bluetiger9/Breeze-SmartSensorHub/Models/earthquake_data/s2-01-Y-scale-100cms2-300sec.png

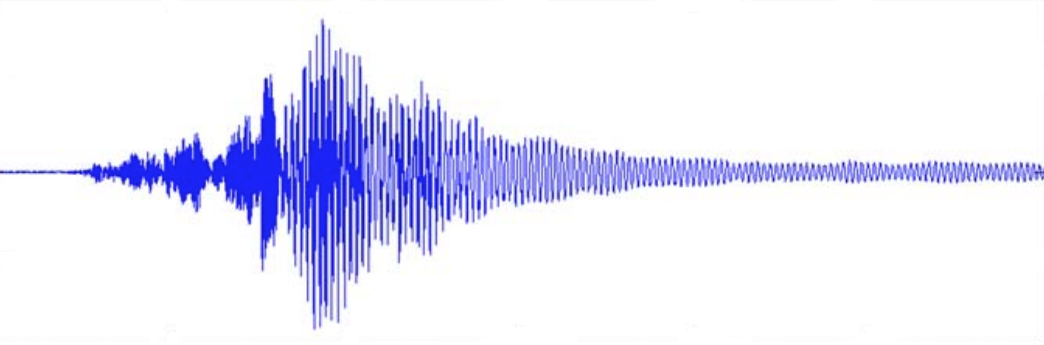
Models/earthquake_data/s2-01-Y-scale-100cms2-300sec.png
