bluetiger9/Breeze-SmartSensorHub/Models/earthquake_data/s1-01-Y-scale-1G-60sec.png

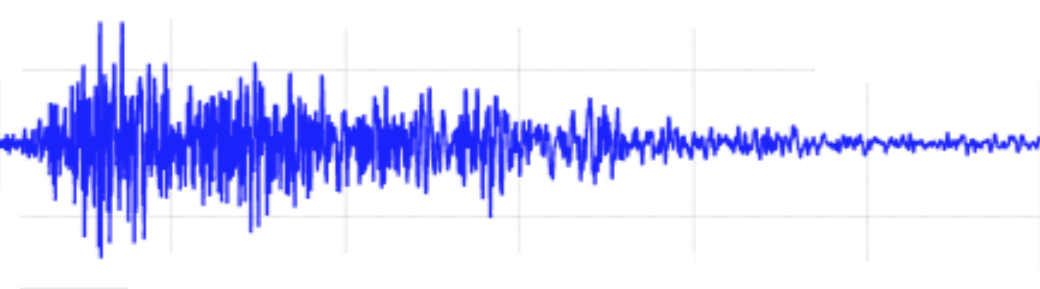
Models/earthquake_data/s1-01-Y-scale-1G-60sec.png
