bluetiger9/Breeze-SmartSensorHub/Models/earthquake_data/s1-02-X-scale-0.4G-60sec.png

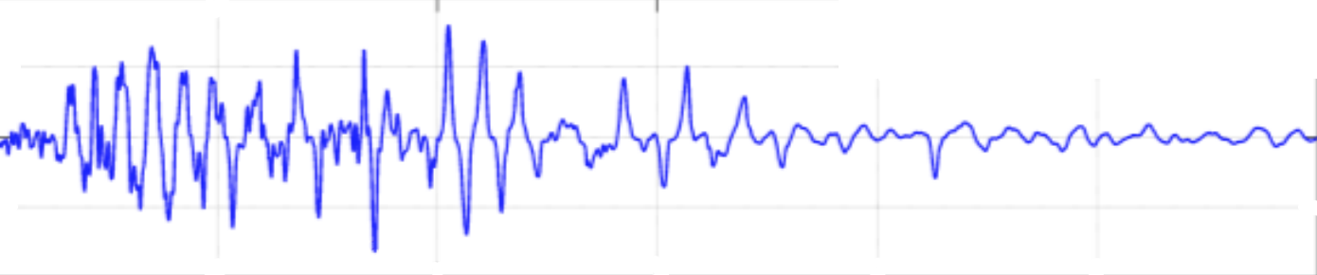
Models/earthquake_data/s1-02-X-scale-0.4G-60sec.png
