bluetiger9/Breeze-SmartSensorHub/Models/earthquake_data/s1-02-Z-scale-0.2G-60sec.png

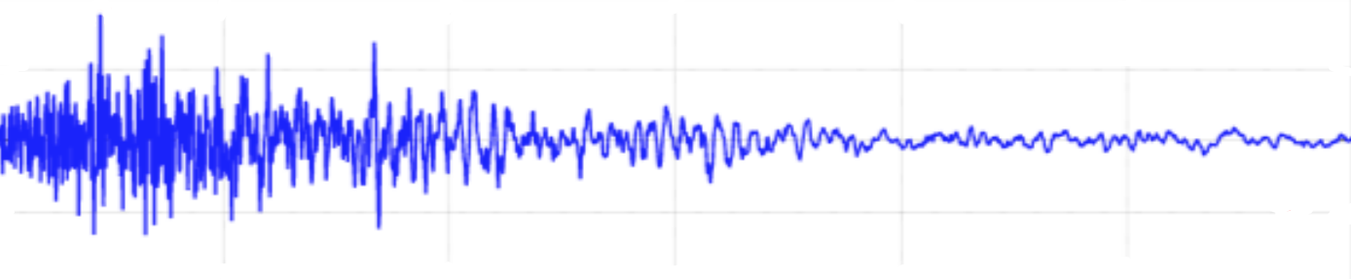
Models/earthquake_data/s1-02-Z-scale-0.2G-60sec.png
