bluetiger9/Breeze-SmartSensorHub/Models/earthquake_data/s3-01-Y-scale-0.34cms2-120sec.png

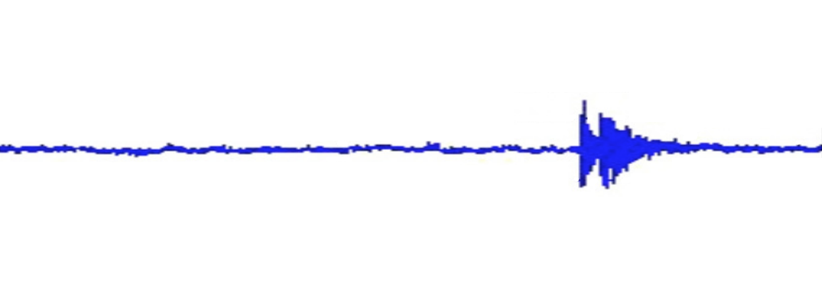
Models/earthquake_data/s3-01-Y-scale-0.34cms2-120sec.png
