bluetiger9/Breeze-SmartSensorHub/Models/earthquake_data/s4-02-XYZ-scale-0.75g-50sec.png

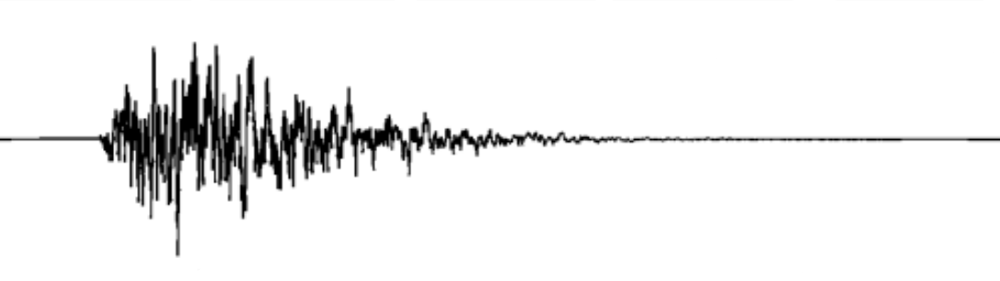
Models/earthquake_data/s4-02-XYZ-scale-0.75g-50sec.png
