bluetiger9/Breeze-SmartSensorHub/Models/earthquake_data/s5-01-Z-scale-150cms2-70sec.png

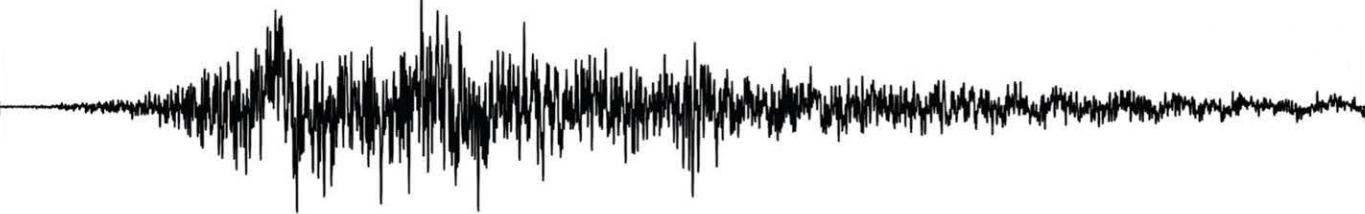
Models/earthquake_data/s5-01-Z-scale-150cms2-70sec.png
