bluetiger9/Breeze-SmartSensorHub/Models/earthquake_data/s5-02-X-scale-150cms2-70sec.png

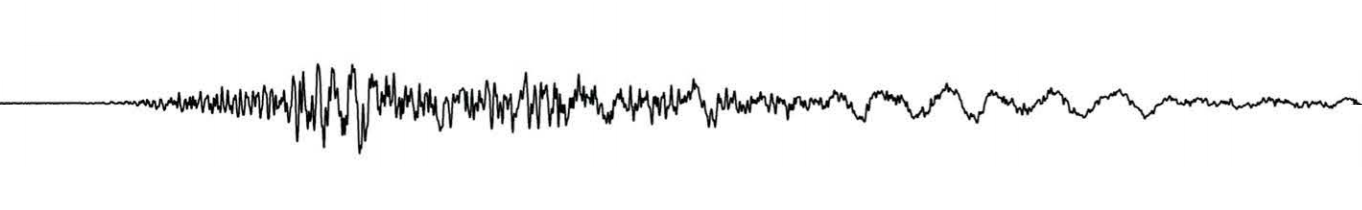
Models/earthquake_data/s5-02-X-scale-150cms2-70sec.png
