bluetiger9/Breeze-SmartSensorHub/Firmware/inc/fpga_gpio_top_bit.h

#include <stdint.h>

uint32_t	axFPGABitStream_GPIO[] = {
	0x00000000, 0x00000000, 0x00000000, 0x00000000, 0x00000000, 0x00000000, 0x00000000, 0x00000000, 0x00000000, 0x00000020, 
	0x00000000, 0x00000000, 0x00000000, 0x00000000, 0x00000020, 0x00000000, 0x00000000, 0x00000000, 0x00000000, 0x00000000, 
	0x00000000, 0x00000000, 0x00000000, 0x00000000, 0x00000000, 0x00000000, 0x00000000, 0x00000000, 0x00000000, 0x00000000, 
	0x00000000, 0x00000000, 0x00000000, 0x00000000, 0x00000000, 0x00000000, 0x00000000, 0x00000020, 0x00000000, 0x00000000, 
	0x00000000, 0x00000000, 0x00000000, 0x00000000, 0x00000000, 0x00000080, 0x00000000, 0x00000000, 0x00000000, 0x00000000, 
	0x00000000, 0x00000000, 0x00000000, 0x00000000, 0x00000000, 0x00000000, 0x00000000, 0x00000000, 0x00000000, 0x00000000, 
	0x00000000, 0x00000000, 0x00000000, 0x00000000, 0x00000000, 0x00000000, 0x00000000, 0x00000000, 0x00000000, 0x00000000, 
	0x00000000, 0x00000000, 0x00000000, 0x00000000, 0x00000000, 0x00000000, 0x00000000, 0x00000000, 0x00000000, 0x00000000, 
	0x00000000, 0x00000000, 0x00000000, 0x00000000, 0x00000000, 0x00000000, 0x00000000, 0x00000000, 0x00000000, 0x00000000, 
	0x00000000, 0x00000000, 0x00000000, 0x00000000, 0x00000000, 0x00000000, 0x00000008, 0x00000000, 0x00000000, 0x00000000, 
	0x00000000, 0x00000000, 0x00000002, 0x00000004, 0x00000004, 0x00000000, 0x00000000, 0x00000002, 0x00000000, 0x00000000, 
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
	0x40004c5c, 0x00000830,
	0x40004c60, 0x00000830,
	0x40004c64, 0x00000830,
	0x40004c68, 0x00000830,
	0x40004c6c, 0x00000830,
	0x40004c70, 0x00000830,
	0x40004c74, 0x00000830,
	0x40004c78, 0x00000830,
	0x40004c7c, 0x00000830,
	0x40004d80, 0xffffffff,
	0x40004d84, 0x00000000
};
