bluetiger9/Breeze-SmartSensorHub/Firmware/src/pincfg_table.c

/*==========================================================
 * Copyright 2020 QuickLogic Corporation
 *
 * Licensed under the Apache License, Version 2.0 (the "License");
 * you may not use this file except in compliance with the License.
 * You may obtain a copy of the License at
 *
 *    http://www.apache.org/licenses/LICENSE-2.0
 *
 * Unless required by applicable law or agreed to in writing, software
 * distributed under the License is distributed on an "AS IS" BASIS,
 * WITHOUT WARRANTIES OR CONDITIONS OF ANY KIND, either express or implied.
 * See the License for the specific language governing permissions and
 * limitations under the License.
 *==========================================================*/

#include "Fw_global_config.h"
#include "eoss3_hal_pad_config.h"
#include "eoss3_hal_gpio.h"

PadConfig pincfg_table[] = 
{
  { // setup UART TX
    .ucPin = PAD_44,
    .ucFunc = PAD44_FUNC_SEL_UART_TXD,
    .ucCtrl = PAD_CTRL_SRC_A0,
    .ucMode = PAD_MODE_OUTPUT_EN,
    .ucPull = PAD_NOPULL,
    .ucDrv = PAD_DRV_STRENGHT_4MA,
    .ucSpeed = PAD_SLEW_RATE_SLOW,
    .ucSmtTrg = PAD_SMT_TRIG_DIS,
  },
  { // setup UART RX
    .ucPin = PAD_45,                     // Options: 14, 16, 25, or 45
    .ucFunc = PAD45_FUNC_SEL_UART_RXD,
    .ucCtrl = PAD_CTRL_SRC_A0,
    .ucMode = PAD_MODE_INPUT_EN,
    .ucPull = PAD_NOPULL,
  },



  { // setup debug input pins Pad 14 - S3_SW_DP_CLK
    .ucMode = PAD_MODE_INPUT_EN,
    .ucCtrl = PAD_CTRL_SRC_OTHER,
    .ucDrv = PAD_DRV_STRENGHT_4MA,
    .ucSpeed = PAD_SLEW_RATE_SLOW,
    .ucSmtTrg = PAD_SMT_TRIG_DIS,
    .ucPin = PAD_14,
    .ucFunc = PAD14_FUNC_SEL_SW_DP_CLK,
    .ucPull = PAD_NOPULL,
  },

  { //setup debug input pins Pad 15 - S3_SW_DP_IO
    .ucMode = PAD_MODE_INPUT_EN,
    .ucCtrl = PAD_CTRL_SRC_OTHER,
    .ucDrv = PAD_DRV_STRENGHT_4MA,
    .ucSpeed = PAD_SLEW_RATE_SLOW,
    .ucSmtTrg = PAD_SMT_TRIG_DIS,
    .ucPin = PAD_15,
    .ucFunc = PAD15_FUNC_SEL_SW_DP_IO,
    .ucPull = PAD_NOPULL
  },

  {
    //Currently Pad 9 is not configured and has an internal pull-down and is 
    // connected to SWD_DATA that has an external pull-up
    //Pad 9 - remove default pull-down configuration, ensure pin is configured as input
    .ucPin = PAD_9,
    .ucFunc = PAD9_FUNC_SEL_GPIO_1,
    .ucMode = PAD_MODE_INPUT_EN,
    .ucPull = PAD_NOPULL,
    .ucDrv = PAD_DRV_STRENGHT_4MA,
    .ucSpeed = PAD_SLEW_RATE_SLOW,
    .ucSmtTrg = PAD_SMT_TRIG_DIS
  },
#if 0
  {  // configure SCL0
    .ucPin = PAD_0,
    .ucFunc = PAD0_FUNC_SEL_SCL_0,
    .ucCtrl = PAD_CTRL_SRC_OTHER,
    .ucMode = PAD_MODE_INPUT_EN,
    .ucPull = PAD_PULLUP,
    .ucDrv = PAD_DRV_STRENGHT_4MA,
    .ucSpeed = PAD_SLEW_RATE_SLOW,
    .ucSmtTrg = PAD_SMT_TRIG_DIS,
  },

  {  // configure SDA0
    .ucPin = PAD_1,
    .ucFunc = PAD1_FUNC_SEL_SDA_0,
    .ucCtrl = PAD_CTRL_SRC_OTHER,
    .ucMode = PAD_MODE_INPUT_EN,
    .ucPull = PAD_PULLUP,
    .ucDrv = PAD_DRV_STRENGHT_4MA,
    .ucSpeed = PAD_SLEW_RATE_SLOW,
    .ucSmtTrg = PAD_SMT_TRIG_DIS,
  },
#endif
  // LEDS
//   { // setup blue LED
//    .ucPin = PAD_18,
//    .ucFunc = PAD18_FUNC_SEL_GPIO_4,
//    .ucCtrl = PAD_CTRL_SRC_A0,
//    .ucMode = PAD_MODE_OUTPUT_EN,
//    .ucPull = PAD_NOPULL,
//    .ucDrv = PAD_DRV_STRENGTH_4MA,
//    .ucSpeed = PAD_SLEW_RATE_SLOW,
//    .ucSmtTrg = PAD_SMT_TRIG_DIS,
//  },
  { // setup green LED
    .ucPin = PAD_21,
    .ucFunc = PAD21_FUNC_SEL_GPIO_5,
    .ucCtrl = PAD_CTRL_SRC_A0,
    .ucMode = PAD_MODE_OUTPUT_EN,
    .ucPull = PAD_NOPULL,
    .ucDrv = PAD_DRV_STRENGTH_4MA,
    .ucSpeed = PAD_SLEW_RATE_SLOW,
    .ucSmtTrg = PAD_SMT_TRIG_DIS,
  },
  { // setup red LED
    .ucPin = PAD_22,
    .ucFunc = PAD22_FUNC_SEL_GPIO_6,
    .ucCtrl = PAD_CTRL_SRC_A0,
    .ucMode = PAD_MODE_OUTPUT_EN,
    .ucPull = PAD_NOPULL,
    .ucDrv = PAD_DRV_STRENGTH_4MA,
    .ucSpeed = PAD_SLEW_RATE_SLOW,
    .ucSmtTrg = PAD_SMT_TRIG_DIS,
  },
  
//   {
//    // Pad6 is the user button
//    .ucPin = PAD_6,
//    .ucFunc = PAD6_FUNC_SEL_GPIO_0,
//    .ucMode = PAD_MODE_INPUT_EN,
//    .ucPull = PAD_PULLUP,
//    .ucDrv = PAD_DRV_STRENGTH_4MA,
//    .ucSpeed = PAD_SLEW_RATE_SLOW,
//    .ucSmtTrg = PAD_SMT_TRIG_DIS
//  },

  
   { // Pad 33 -- Test clock
    .ucPin = PAD_33,
    .ucFunc = PAD33_FUNC_SEL_FBIO_33,
    .ucCtrl = PAD_CTRL_SRC_FPGA,
    .ucMode = PAD_MODE_OUTPUT_EN,
    .ucPull = PAD_NOPULL,
    .ucDrv = PAD_DRV_STRENGHT_4MA,
    .ucSpeed = PAD_SLEW_RATE_SLOW,
    .ucSmtTrg = PAD_SMT_TRIG_DIS,
  },
  
  // SPI Master
   { // Pad 34 -- SPI Master CLK
    .ucPin = PAD_34,
    .ucFunc = PAD34_FUNC_SEL_FBIO_34,
    .ucCtrl = PAD_CTRL_SRC_FPGA,
    .ucMode = PAD_MODE_OUTPUT_EN,
    .ucPull = PAD_NOPULL,
    .ucDrv = PAD_DRV_STRENGHT_4MA,
    .ucSpeed = PAD_SLEW_RATE_SLOW,
    .ucSmtTrg = PAD_SMT_TRIG_DIS,
  },
  { // Pad 38 -- SPI Master MOSI
    .ucPin = PAD_38,
    .ucFunc = PAD38_FUNC_SEL_FBIO_38,
    .ucCtrl = PAD_CTRL_SRC_FPGA,
    .ucMode = PAD_MODE_OUTPUT_EN,
    .ucPull = PAD_NOPULL,
    .ucDrv = PAD_DRV_STRENGHT_4MA,
    .ucSpeed = PAD_SLEW_RATE_SLOW,
    .ucSmtTrg = PAD_SMT_TRIG_DIS,
  },
  { // Pad 39 -- SPI Master SSn1
    .ucPin = PAD_39,
    .ucFunc = PAD39_FUNC_SEL_FBIO_39,
    .ucCtrl = PAD_CTRL_SRC_FPGA,
    .ucMode = PAD_MODE_OUTPUT_EN,
    .ucPull = PAD_NOPULL,
    .ucDrv = PAD_DRV_STRENGHT_4MA,
    .ucSpeed = PAD_SLEW_RATE_SLOW,
    .ucSmtTrg = PAD_SMT_TRIG_DIS,
  },
   { // Pad 36 -- SPI Master MISO
    .ucPin = PAD_36,
    .ucFunc = PAD36_FUNC_SEL_FBIO_36,
    .ucCtrl = PAD_CTRL_SRC_FPGA,
    .ucMode = PAD_MODE_INPUT_EN,
    .ucPull = PAD_NOPULL,
  },
  
  //------------- USB ---------------//
   { // Pad 37 -- USB Pullup control
    .ucPin = PAD_37,
    .ucFunc = PAD37_FUNC_SEL_FBIO_37,
    .ucCtrl = PAD_CTRL_SRC_FPGA,
    .ucMode = PAD_MODE_OUTPUT_EN,
    .ucPull = PAD_NOPULL,
    .ucDrv = PAD_DRV_STRENGHT_4MA,
    .ucSpeed = PAD_SLEW_RATE_SLOW,
    .ucSmtTrg = PAD_SMT_TRIG_DIS,
  },
  { // Pad 41 -- USB D-
    .ucPin = PAD_41,
    .ucFunc = PAD41_FUNC_SEL_FBIO_41,
    .ucCtrl = PAD_CTRL_SRC_FPGA,
    .ucMode = PAD_MODE_OUTPUT_EN,
    .ucPull = PAD_NOPULL,
    .ucDrv = PAD_DRV_STRENGHT_4MA,
    .ucSpeed = PAD_SLEW_RATE_SLOW,
    .ucSmtTrg = PAD_SMT_TRIG_DIS,
  },
  { // Pad 41 -- USB D+
    .ucPin = PAD_42,
    .ucFunc = PAD42_FUNC_SEL_FBIO_42,
    .ucCtrl = PAD_CTRL_SRC_FPGA,
    .ucMode = PAD_MODE_OUTPUT_EN,
    .ucPull = PAD_NOPULL,
    .ucDrv = PAD_DRV_STRENGHT_4MA,
    .ucSpeed = PAD_SLEW_RATE_SLOW,
    .ucSmtTrg = PAD_SMT_TRIG_DIS,
  },

#if (SENSOR_SSSS_RATE_DEBUG_GPIO)
  { // setup GPIO for toggling whenever a datablock is dispatched to UART
    .ucPin = PAD_11,
    .ucFunc = PAD11_FUNC_SEL_GPIO_2,
    .ucCtrl = PAD_CTRL_SRC_A0,
    .ucMode = PAD_MODE_OUTPUT_EN,
    .ucPull = PAD_NOPULL,
    .ucDrv = PAD_DRV_STRENGTH_4MA,
    .ucSpeed = PAD_SLEW_RATE_SLOW,
    .ucSmtTrg = PAD_SMT_TRIG_DIS,
  },
#else
  { // IO_11 / GPIO(2) - CS_AQ
    .ucPin = PAD_11,
    .ucFunc = PAD11_FUNC_SEL_GPIO_2,
    .ucCtrl = PAD_CTRL_SRC_A0,
    .ucMode = PAD_MODE_OUTPUT_EN,
    .ucPull = PAD_NOPULL,
    .ucDrv = PAD_DRV_STRENGTH_4MA,
    .ucSpeed = PAD_SLEW_RATE_SLOW,
    .ucSmtTrg = PAD_SMT_TRIG_DIS,
  },
#endif
  { // IO_30 / GPIO(3) - CS_UV
    .ucPin = PAD_30,
    .ucFunc = PAD30_FUNC_SEL_GPIO_3,
    .ucCtrl = PAD_CTRL_SRC_A0,
    .ucMode = PAD_MODE_OUTPUT_EN,
    .ucPull = PAD_NOPULL,
    .ucDrv = PAD_DRV_STRENGTH_4MA,
    .ucSpeed = PAD_SLEW_RATE_SLOW,
    .ucSmtTrg = PAD_SMT_TRIG_DIS,
  },
  { // IO_24 / GPIO(0) - CS_COM
    .ucPin = PAD_24,
    .ucFunc = PAD24_FUNC_SEL_GPIO_0,
    .ucCtrl = PAD_CTRL_SRC_A0,
    .ucMode = PAD_MODE_OUTPUT_EN,
    .ucPull = PAD_NOPULL,
    .ucDrv = PAD_DRV_STRENGTH_4MA,
    .ucSpeed = PAD_SLEW_RATE_SLOW,
    .ucSmtTrg = PAD_SMT_TRIG_DIS,
  },
  { // IO_23 / GPIO(7) - CS_COM (??? - hangging)
    .ucPin = PAD_23,
    .ucFunc = PAD23_FUNC_SEL_GPIO_7,
    .ucCtrl = PAD_CTRL_SRC_A0,
    .ucMode = PAD_MODE_OUTPUT_EN,
    .ucPull = PAD_NOPULL,
    .ucDrv = PAD_DRV_STRENGTH_4MA,
    .ucSpeed = PAD_SLEW_RATE_SLOW,
    .ucSmtTrg = PAD_SMT_TRIG_DIS,
  },
  { // IO_24 / GPIO(0) - CS_COM
    .ucPin = PAD_31,
    .ucFunc = PAD31_FUNC_SEL_GPIO_4,
    .ucCtrl = PAD_CTRL_SRC_A0,
    .ucMode = PAD_MODE_OUTPUT_EN,
    .ucPull = PAD_NOPULL,
    .ucDrv = PAD_DRV_STRENGTH_4MA,
    .ucSpeed = PAD_SLEW_RATE_SLOW,
    .ucSmtTrg = PAD_SMT_TRIG_DIS,
  },

  { // IO_2 / FBIO(2) - PWR_COM
    .ucPin = PAD_2,
    .ucFunc = PAD2_FUNC_SEL_FBIO_2,
    .ucCtrl = PAD_CTRL_SRC_FPGA,
    .ucMode = PAD_MODE_OUTPUT_EN,
    .ucPull = PAD_NOPULL,
    .ucDrv = PAD_DRV_STRENGTH_4MA,
    .ucSpeed = PAD_SLEW_RATE_SLOW,
    .ucSmtTrg = PAD_SMT_TRIG_DIS,
  },

  { // IO_12 / FBIO(12) - PWR_COM
    .ucPin = PAD_12,
    .ucFunc = PAD12_FUNC_SEL_FBIO_12,
    .ucCtrl = PAD_CTRL_SRC_FPGA,
    .ucMode = PAD_MODE_OUTPUT_EN,
    .ucPull = PAD_NOPULL,
    .ucDrv = PAD_DRV_STRENGTH_4MA,
    .ucSpeed = PAD_SLEW_RATE_SLOW,
    .ucSmtTrg = PAD_SMT_TRIG_DIS,
  },

#if (AUDIO_DRIVER == 1) && (PDM_PAD_28_29 == 1)
  { // Pad 28 -- PDM DATA
    .ucPin = PAD_28,
    .ucFunc = PAD28_FUNC_SEL_PDM_DIN,
    .ucCtrl = PAD_CTRL_SRC_A0,
    .ucMode = PAD_MODE_INPUT_EN,
    .ucPull = PAD_NOPULL,
    .ucDrv = PAD_DRV_STRENGHT_4MA,
    .ucSpeed = PAD_SLEW_RATE_SLOW,
    .ucSmtTrg = PAD_SMT_TRIG_DIS,
  },
  { // Pad 29 -- PDM CLK
    .ucPin = PAD_29,
    .ucFunc = PAD29_FUNC_SEL_PDM_CKO,
    .ucCtrl = PAD_CTRL_SRC_A0,
    .ucMode = PAD_MODE_OUTPUT_EN,
    .ucPull = PAD_NOPULL,
    .ucDrv = PAD_DRV_STRENGHT_4MA,
    .ucSpeed = PAD_SLEW_RATE_SLOW,
    .ucSmtTrg = PAD_SMT_TRIG_DIS,
  },
#endif
#if  (AUDIO_DRIVER == 1) && (PDM_PAD_8_10 == 1)
  {
    /* Configuring Pad_8 as PDM Clk out*/
    .ucPin = PAD_8;
    .ucFunc = PAD8_FUNC_PDM_CKO;
    .ucCtrl = PAD_CTRL_SRC_A0;
    .ucMode = PAD_MODE_OUTPUT_EN;
    .ucPull = PAD_NOPULL;
    .ucDrv = PAD_DRV_STRENGHT_4MA;
    .ucSpeed = PAD_SLEW_RATE_SLOW;
    .ucSmtTrg = PAD_SMT_TRIG_DIS;
  },
  {
    /* Configuring PAD_10 as PDM Data In*/
    .ucPin = PAD_10;
    .ucFunc = PAD10_FUNC_SEL_PDM_DIN;
    .ucCtrl = PAD_CTRL_SRC_A0;
    .ucMode = PAD_MODE_INPUT_EN;
    .ucPull = PAD_NOPULL;
    .ucDrv = PAD_DRV_STRENGHT_4MA;
    .ucSpeed = PAD_SLEW_RATE_SLOW;
    .ucSmtTrg = PAD_SMT_TRIG_DIS;
  },
#endif

};

GPIOCfgTypeDef  gpiocfg_table[] =
{
  {
    //vm1010 dout setup as hardware interrupt pin on PAD_41 (sensor interrupt 6)  //Chandalar jumper J3.4
    .usPadNum = PAD_41,
    .ucGpioNum = GPIO_6,
    .ucFunc = PAD41_FUNC_SEL_SENS_INT_6,
    .intr_type = EDGE_TRIGGERED,
    .pol_type = RISE_HIGH,
    .ucPull = PAD_PULLDOWN,
  },

};

int sizeof_pincfg_table = sizeof(pincfg_table)/sizeof(pincfg_table[0]);
int sizeof_gpiocfg_table = sizeof(gpiocfg_table)/sizeof(gpiocfg_table[0]);
